thomo/sensornode/multiblink/src/user.h

#ifndef USER_H
#define	USER_H

#include "system.h"

#ifdef	__cplusplus
extern "C" {
#endif /* __cplusplus */

void InitApp(void);         /* I/O and Peripheral Initialization */
void LoopApp(void);

#ifdef	__cplusplus
}
#endif /* __cplusplus */

#endif	/* USER_H */
